danderflieger/aoa_3d_models/Solidworks_Files/Mount_C152_Plastic_Bottom_Back.SLDPRT

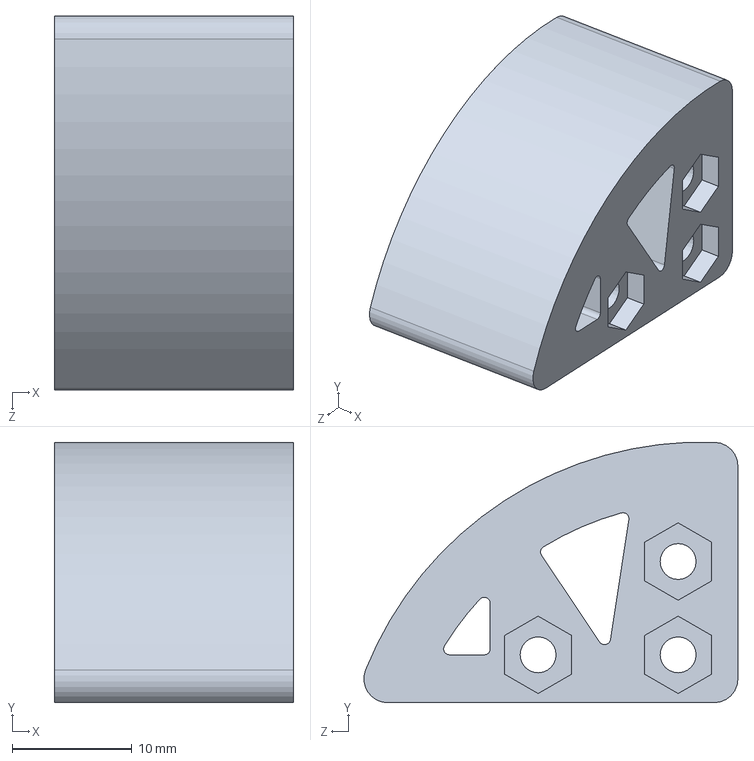
[picture p16: CAD file, 2023-10-14]
Solidworks_Files/Mount_C152_Plastic_Bottom_Back.SLDPRT
20.0 x 21.8 x 31.2 mm
