danderflieger/aoa_3d_models/Solidworks_Files/WindWedgeCounterWeight_v2.SLDPRT

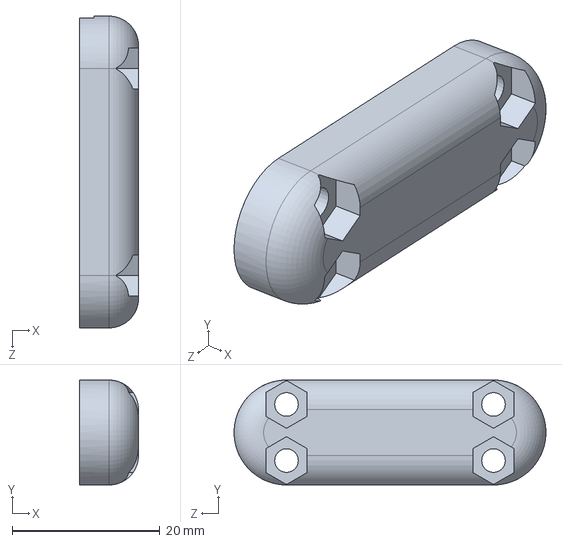
[picture p17: CAD file, 2023-10-14]
Solidworks_Files/WindWedgeCounterWeight_v2.SLDPRT
8.00 x 14.2 x 42.2 mm
