danderflieger/aoa_3d_models/Solidworks_Files/1mmSpacer_v5.SLDPRT

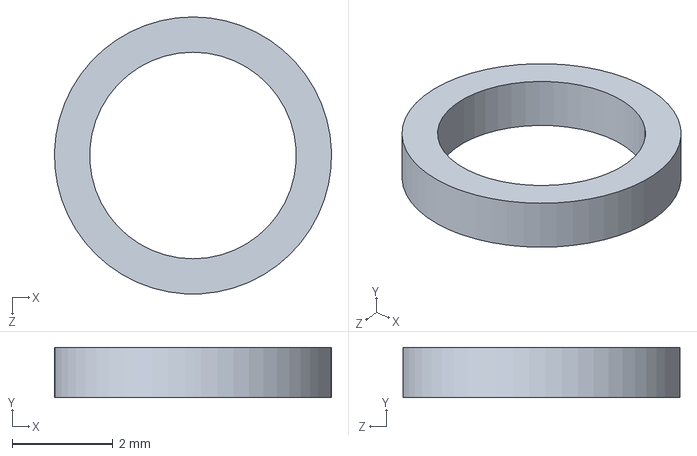
[picture p18: CAD file, 2023-10-14]
Solidworks_Files/1mmSpacer_v5.SLDPRT
5.50 x 1.00 x 5.50 mm
