danderflieger/aoa_3d_models/Solidworks_Files/Mount_C152_Aluminum_Plate.SLDPRT

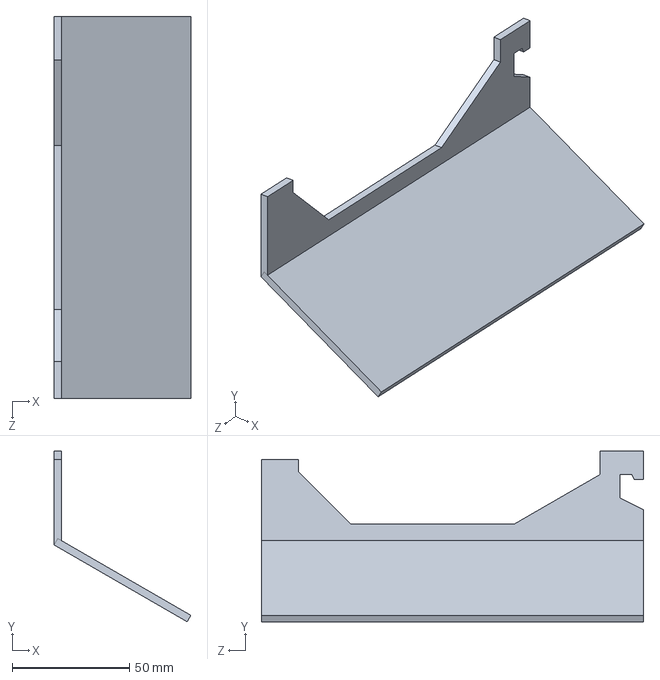
[picture p19: CAD file, 2023-10-14]
Solidworks_Files/Mount_C152_Aluminum_Plate.SLDPRT
58.4 x 72.8 x 163.0 mm
