danderflieger/aoa_3d_models/Solidworks_Files/Mount_C152_Aluminum_Top_Side_Plate.SLDPRT

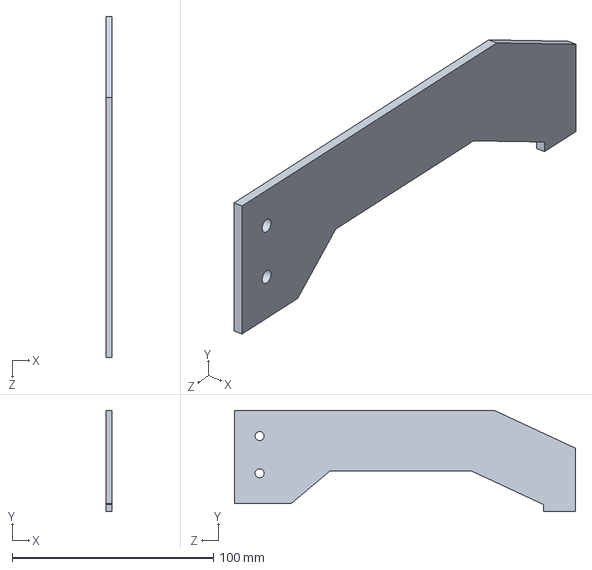
[picture p20: CAD file, 2023-10-14]
Solidworks_Files/Mount_C152_Aluminum_Top_Side_Plate.SLDPRT
3.17 x 50.3 x 169.7 mm
