danderflieger/aoa_3d_models/Solidworks_Files/SmallCarbonFiberTube.SLDPRT

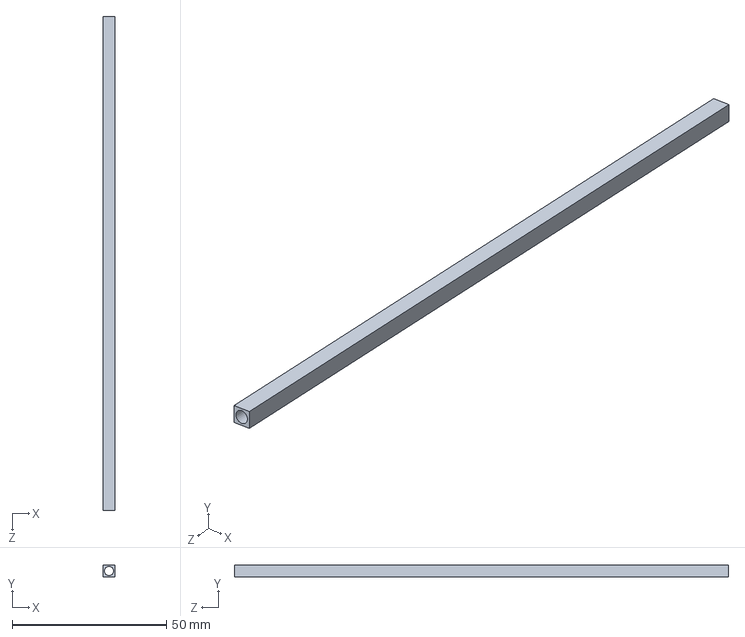
[picture p21: CAD file, 2023-10-14]
Solidworks_Files/SmallCarbonFiberTube.SLDPRT
4.00 x 4.00 x 160.0 mm
