danderflieger/aoa_3d_models/Solidworks_Files/Mount_C152_Aluminum_Bottom_Side_Plate.SLDPRT

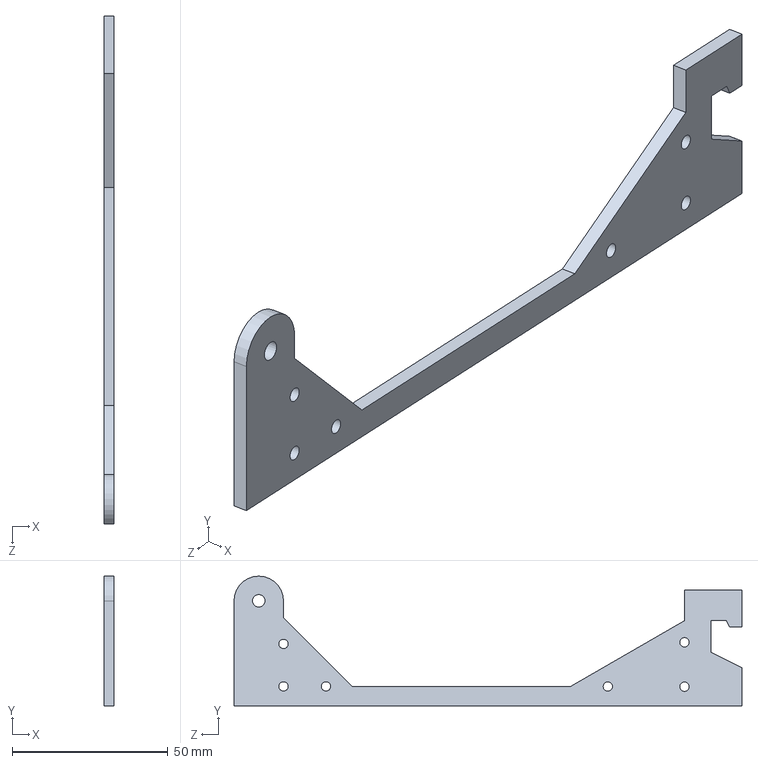
[picture p22: CAD file, 2023-10-14]
Solidworks_Files/Mount_C152_Aluminum_Bottom_Side_Plate.SLDPRT
3.17 x 41.7 x 163.0 mm
