danderflieger/aoa_3d_models/Solidworks_Files/Mount_C152_Aluminum_Side_Pivot.SLDPRT

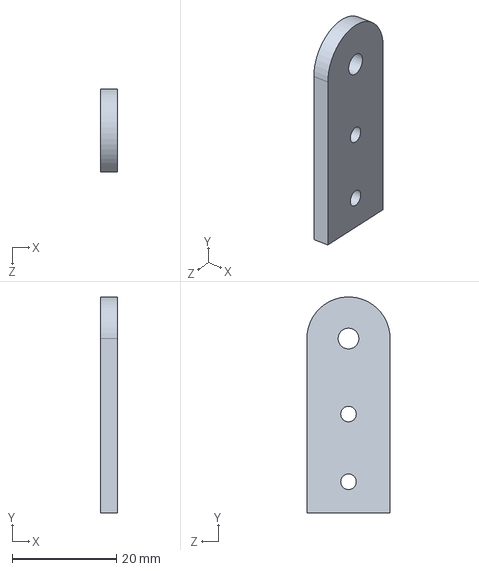
[picture p23: CAD file, 2023-10-14]
Solidworks_Files/Mount_C152_Aluminum_Side_Pivot.SLDPRT
3.17 x 41.5 x 16.0 mm
