danderflieger/aoa_3d_models/Solidworks_Files/Mount_C152_Aluminum_Bottom_Top_Center_Plate.SLDPRT

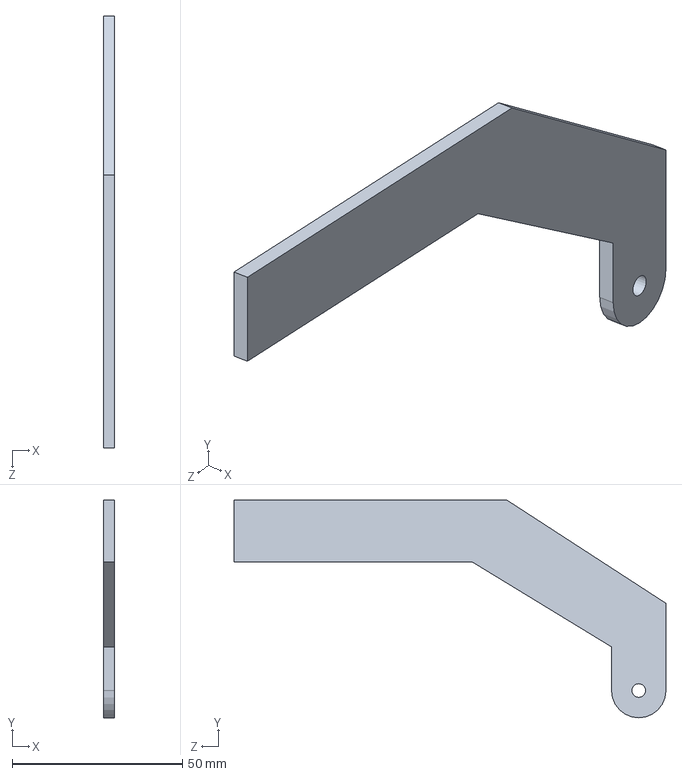
[picture p24: CAD file, 2023-10-14]
Solidworks_Files/Mount_C152_Aluminum_Bottom_Top_Center_Plate.SLDPRT
3.17 x 63.8 x 126.7 mm
